mike-mcmahon/PowerMonitor/src/cellular.cpp

/**
  ******************************************************************************
  * Project:    Power Monitor
  * @file    	  cellular.cpp
  * @author  	  Mike McMahon, Cypress Embedded Systems
  * @brief   	  Implements prototypes in header file cellular.h
  *          	  monitoring cellular and Particle cloud connections.
  *              
  ******************************************************************************
  * @attention
  *
  * <h2><center>&copy; Copyright (c) 2025 Mike McMahon, Cypress Embedded Systems.  All rights reserved.</center></h2>
  *	
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
  ******************************************************************************
  */

#include "Particle.h"
#include "cellular.h"

//For LTE Cellular connection status
bool systemConnected;
bool LTEindicatorFlash;
int onCell;
int cellSearch;

/*
 *  @brief  Check to ensure LTE cellular is still connected.
 *          Note: If cellular connection is lost, the module will attempt to reconnect on its own.  
 *          There is no need for this application code to make the attempt to reconnect.
 *  @param  none
 *  @retval none
 */
void testCellularConnection(void) {
    //check that we are still connected to cellular and the Particle cloud service
	if (Cellular.ready() && Particle.connected()) {
		systemConnected = true;
		digitalWrite(onCell, HIGH);
		digitalWrite(cellSearch, LOW);
	}
	else {
		systemConnected = false;
		digitalWrite(onCell, LOW);
		digitalWrite(cellSearch, HIGH);
	}
}
